KonradWohlfahrt/FocusWheel/V2/src/FocusWheel/tiles.h

/*
    --- BATTERY STATUS TILES ---
*/
const uint8_t _batteryBackgroundNormal[24] PROGMEM = { 0x00,0x00,0x7e,0x81,0x81,0x81,0x81,0x81,
                                              0x81,0x81,0x81,0x81,0x81,0x81,0x81,0x81,
                                              0x81,0x81,0x81,0xc3,0x7e,0x18,0x00,0x00 };
const uint8_t _batteryBackgroundCharging[24] PROGMEM = { 0x00,0x00,0x7e,0x81,0x81,0x81,0x81,0x00,
                                                0x81,0x81,0x81,0x81,0x81,0x81,0x81,0x81,
                                                0x00,0x81,0x81,0xc3,0x7e,0x18,0x00,0x00 };
const uint8_t _batteryOneBar[8] PROGMEM = { 0x00,0x00,0x7e,0x81,0xbd,0xbd,0xbd,0xbd };
const uint8_t _batteryTwoBar[8] PROGMEM = { 0x81,0xbd,0xbd,0xbd,0xbd,0x81,0x81,0x81 };
const uint8_t _batteryThreeBar[16] PROGMEM = { 0x81,0xbd,0xbd,0xbd,0xbd,0x81,0xbd,0xbd,
                                       0xbd,0xbd,0x81,0xc3,0x7e,0x18,0x00,0x00 };
const uint8_t _batteryCharging[8] PROGMEM = { 0x80,0xc8,0x6c,0x7c,0x3e,0x36,0x13,0x1 };
const uint8_t _batteryLow[8] PROGMEM = { 0x0,0x0,0xe,0xdf,0xdf,0xe,0x0,0x0 };
const uint8_t _usbPowered[8] PROGMEM = { 0x24,0x24,0x7e,0x7e,0x7e,0x3c,0x18,0x18 };

/*
    --- STANDARD TILES ---
*/
const uint8_t _emptyTile[8] PROGMEM = { 0x00,0x00,0x00,0x00,0x00,0x00,0x00,0x00 };
const uint8_t _chessboardTile[8] PROGMEM = { 0xaa,0x55,0xaa,0x55,0xaa,0x55,0xaa,0x55 };
const uint8_t _fullTile[8] PROGMEM = { 0xff,0xff,0xff,0xff,0xff,0xff,0xff,0xff };

/*
    --- SLIDER TILES ---
*/
const uint8_t _barLeft[8] PROGMEM = { 0xf0,0xf0,0x90,0x90,0x0,0x0,0x0,0x60 };
const uint8_t _barRight[8] PROGMEM = { 0x60,0x0,0x0,0x0,0x90,0x90,0xf0,0xf0 };
const uint8_t _bar[8] PROGMEM = { 0x60,0x60,0x60,0x60,0x60,0x60,0x60,0x60 };
const uint8_t _barFull[8] PROGMEM = { 0xf0,0xf0,0xf0,0xf0,0xf0,0xf0,0xf0,0xf0 };


/*
    --- SOUND TILES ---
*/
const uint8_t _soundOnTile[8] PROGMEM = { 0x18,0x3c,0x3c,0x7e,0x0,0x18,0x42,0x3c };
const uint8_t _soundOffTile[8] PROGMEM = { 0x18,0x3c,0x3c,0x7e,0x0,0x0,0x0,0x0 };
